Pinoccio/hardware-pinoccio/firmware/bootloader/uracoli-src-20131127/inc/const.h

/* Copyright (c) 2007 - 2013
    Marco Arena
    Axel Wachtler

   All rights reserved.

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
   THIS SOFTWARE IS PROVIDED BY THE COPYRIGHT HOLDERS AND CONTRIBUTORS "AS IS"
   AND ANY EXPRESS OR IMPLIED WARRANTIES, INCLUDING, BUT NOT LIMITED TO, THE
   IMPLIED WARRANTIES OF MERCHANTABILITY AND FITNESS FOR A PARTICULAR PURPOSE
   ARE DISCLAIMED. IN NO EVENT SHALL THE COPYRIGHT OWNER OR CONTRIBUTORS BE
   LIABLE FOR ANY DIRECT, INDIRECT, INCIDENTAL, SPECIAL, EXEMPLARY, OR
   CONSEQUENTIAL DAMAGES (INCLUDING, BUT NOT LIMITED TO, PROCUREMENT OF
   SUBSTITUTE GOODS OR SERVICES; LOSS OF USE, DATA, OR PROFITS; OR BUSINESS
   INTERRUPTION) HOWEVER CAUSED AND ON ANY THEORY OF LIABILITY, WHETHER IN
   CONTRACT, STRICT LIABILITY, OR TORT (INCLUDING NEGLIGENCE OR OTHERWISE)
   ARISING IN ANY WAY OUT OF THE USE OF THIS SOFTWARE, EVEN IF ADVISED OF THE
   POSSIBILITY OF SUCH DAMAGE. */

/* $Id$ */
/**
 * @file
 * @brief General Definitions.
 *
 */
/*====================================================================*/
#ifndef CONST_H
#define CONST_H
#include <stdint.h>
#include <stdbool.h>

/*=== board type constants ===================================================*/
/**
 * @addtogroup grpBoard
 * @{
 */

#define BOARD_NONE (0)

/* the legacy boards are sorted alphabetically */
#define BOARD_ANY2400 (1)
#define BOARD_ANY2400ST (2)
#define BOARD_ANY900 (3)
#define BOARD_ANY900ST (4)
#define BOARD_BAT (5)
#define BOARD_BITBEAN (6)
#define BOARD_CBB212 (7)
#define BOARD_CBB230 (8)
#define BOARD_CBB230B (9)
#define BOARD_CBB231 (10)
#define BOARD_CBB232 (11)
#define BOARD_CBB233 (12)
#define BOARD_DERFA1 (13)
#define BOARD_DERFTORCBRFA1 (14)
#define BOARD_DRACULA (15)
#define BOARD_IBDT212 (16)
#define BOARD_IBDT231 (17)
#define BOARD_IBDT232 (18)
#define BOARD_ICM230_11 (19)
#define BOARD_ICM230_12A (20)
#define BOARD_ICM230_12B (21)
#define BOARD_ICM230_12C (22)
#define BOARD_ICS230_11 (23)
#define BOARD_ICS230_12 (24)
#define BOARD_ICT230 (25)
#define BOARD_IM240A (26)
#define BOARD_IM240A_EVAL (27)
#define BOARD_LGEE231 (28)
#define BOARD_LGEE231_V2 (29)
#define BOARD_MIDGEE (30)
#define BOARD_MNB900 (31)
#define BOARD_MUSE231 (32)
#define BOARD_MUSEII232 (33)
#define BOARD_MUSEIIRFA (34)
#define BOARD_PINOCCIO (35)
#define BOARD_PSK212 (36)
#define BOARD_PSK230 (37)
#define BOARD_PSK230B (38)
#define BOARD_PSK231 (39)
#define BOARD_PSK232 (40)
#define BOARD_PSK233 (41)
#define BOARD_RADIOFARO (42)
#define BOARD_RADIOFARO_V1 (43)
#define BOARD_RAVRF230A (44)
#define BOARD_RAVRF230B (45)
#define BOARD_RBB128RFA1 (46)
#define BOARD_RBB212 (47)
#define BOARD_RBB230 (48)
#define BOARD_RBB230B (49)
#define BOARD_RBB231 (50)
#define BOARD_RBB232 (51)
#define BOARD_RBB233 (52)
#define BOARD_RDK212 (53)
#define BOARD_RDK230 (54)
#define BOARD_RDK230B (55)
#define BOARD_RDK231 (56)
#define BOARD_RDK232 (57)
#define BOARD_RDK233 (58)
#define BOARD_ROSE231 (59)
#define BOARD_RZUSB (60)
#define BOARD_STB128RFA1 (61)
#define BOARD_STB212 (62)
#define BOARD_STB230 (63)
#define BOARD_STB230B (64)
#define BOARD_STB231 (65)
#define BOARD_STB232 (66)
#define BOARD_STB233 (67)
#define BOARD_STKM16 (68)
#define BOARD_STKM8 (69)
#define BOARD_TINY230 (70)
#define BOARD_TINY231 (71)
#define BOARD_WDBA1281 (72)
#define BOARD_WPROG (73)
#define BOARD_XXO (74)
#define BOARD_ZGBH212 (75)
#define BOARD_ZGBH230 (76)
#define BOARD_ZGBH231 (77)
#define BOARD_ZGBL212 (78)
#define BOARD_ZGBL230 (79)
#define BOARD_ZGBL231 (80)
#define BOARD_ZGBT1281A2NOUART (81)
#define BOARD_ZGBT1281A2UART0 (82)
#define BOARD_ZGBT1281A2UART1 (83)
#define BOARD_ZIGDUINO (84)

/* beyond this point the boards are added chronologically */
#define BOARD_STB256RFR2 (85)
#define BOARD_RASPBEE (86)
#define BOARD_DERFN256U0 (87)
#define BOARD_DERFN256U0PA (88)
#define BOARD_DERFN128 (89)
#define BOARD_DERFN128U0 (90)

#define BOARD_LAST (BOARD_RASPBEE)
/** @} */

/**
 * @addtogroup grpRadio
 * @{
 */

/*=== radio constants ================================================*/
#define  RADIO_AT86RF230 (1) /**< Identifier for radio AT86RF230 */
#define  RADIO_AT86RF230A (RADIO_AT86RF230) /**< Identifier for radio AT86RF230 Rev A */
#define  RADIO_AT86RF230B (2) /**< Identifier for radio AT86RF230 Rev B */
#define  RADIO_AT86RF231 (3) /**< Identifier for radio AT86RF231 */
#define  RADIO_AT86RF212 (4) /**< Identifier for radio AT86RF212 */
#define  RADIO_ATMEGA128RFA1_A (5) /**< Identifier for radio ATmega128RFA1 Rev. A */
#define  RADIO_ATMEGA128RFA1_B (6) /**< Identifier for radio ATmega128RFA1 Rev. B */
#define  RADIO_ATMEGA128RFA1_C (7) /**< Identifier for radio ATmega128RFA1 Rev. C */
#define  RADIO_ATMEGA128RFA1_D (8) /**< Identifier for radio ATmega128RFA1 Rev. D */
#define  RADIO_AT86RF232 (9) /**< Identifier for radio AT86RF232 */
#define  RADIO_AT86RF233 (10) /**< Identifier for radio AT86RF233 */
#define  RADIO_ATMEGA256RFR2 (11) /**< Identifier for radio ATmega128RFR2 */

#define RADIO_BAND_700 (1) /**< 700MHz frequency band (china) */
#define RADIO_BAND_800 (2) /**< 868MHz frequency band (europe)*/
#define RADIO_BAND_900 (3) /**< 900MHz frequency band (north america)*/
#define RADIO_BAND_2400 (4)  /**< 2.4GHz frequency band (international)*/

/*=== modulation schemes =====================================================*/
#define MOD_BPSK_20    (0) /**< PHY modulation BPSK, 20 kbit/s */
#define MOD_BPSK_40    (1) /**< PHY modulation BPSK, 40 kbit/s */
#define MOD_OQPSK_100  (2) /**< PHY modulation O-QPSK, 100 kbit/s */
#define MOD_OQPSK_200  (3) /**< PHY modulation O-QPSK, 200 kbit/s */
#define MOD_OQPSK_250  (4) /**< PHY modulation O-QPSK, 250 kbit/s */
#define MOD_OQPSK_400  (5) /**< PHY modulation O-QPSK, 400 kbit/s */
#define MOD_OQPSK_500  (6) /**< PHY modulation O-QPSK, 500 kbit/s */
#define MOD_OQPSK_1000 (7) /**< PHY modulation O-QPSK, 1000 kbit/s */
#define MOD_OQPSK_2000 (8) /**< PHY modulation O-QPSK, 2000 kbit/s */

/* === sensor types ========================================================= */

typedef uint8_t sensor_const_t;

#define SENSOR_MCU_T (1)
#define SENSOR_MCU_VTG (2)
#define SENSOR_SHT21_RH (3)
#define SENSOR_SHT21_T (4)
#define SENSOR_ADXL345_ACC (5)
#define SENSOR_MMA7455_ACC (5)

/** @} */

/**
 * @addtogroup grpHIF
 * @{
 */

/*=== HIF type constants =====================================================*/
#define  HIF_NONE     (0)  /**< Identifier for no host interface */
#define  HIF_UART_0   (10) /**< Identifier for HIF type UART 0 */
#define  HIF_UART_1   (11) /**< Identifier for HIF type UART 1 */
#define  HIF_FT245    (20) /**< Identifier for HIF type USB/FT245*/
#define  HIF_AT90USB  (21) /**< Identifier for HIF type USB/ATmega1287 */

/*=== USB constants ==========================================================*/
/**
 * uracoli USB Vendor ID
 *
 * The pair of the uracoli vendor id, device id are obtained by
 *
 *  - http://www.voti.nl/pids/
 *  - http://www.frank-buss.de/pid.txt
 */
#define URACOLI_USB_VID (5824)
/**
 * uracoli USB Product ID
 * see also @ref USB_VID_URACOLI
 */
#define URACOLI_USB_PID (2183)

#define URACOLI_USB_BCD_RELEASE (0x100)
#define URACOLI_USB_VENDOR_NAME  L"URACOLI"
#define URACOLI_USB_PRODUCT_NAME L"RZUSBSTICK"

/** @} */

/**
 * @addtogroup grpTrx
 * @{
 */

/*=== spi constants ==========================================================*/
#define SPI_RATE_1_2      (4) /**< SPI clock running is 0.5 (1/2) of cpu clock */
#define SPI_RATE_1_4      (0) /**< SPI clock running is 0.25 (1/4) of cpu clock */
#define SPI_RATE_1_8      (5) /**< SPI clock running is 0.125 (1/8) of cpu clock */
#define SPI_RATE_1_16     (1) /**< SPI clock running is 0.0635 (1/16) of cpu clock */
#define SPI_RATE_1_32     (6) /**< SPI clock running is 0.03125 (1/32)of cpu clock */
#define SPI_RATE_1_64     (2) /**< SPI clock running is 0.015625 (1/64)of cpu clock */
#define SPI_RATE_1_128    (3) /**< SPI clock running is 0.0078125 (1/128) of cpuclock */

/** @} */


#if defined (DOXYGEN)
/** macro that forces an enumeration to use 8 bit instead of 16 bit integers. */
#define SHORTENUM
#else
#define SHORTENUM  __attribute__((packed))
#endif

/**
 * @addtogroup grpTrx
 * @{
 */
#define FCTL_DATA _BV(0)        /**< data frame fype in frame control field */
#define FCTL_ACK  _BV(5)        /**< ack request in frame control field */
#define FCTL_IPAN _BV(6)        /**< intra pan bit in frame control field */
#define FCTL_DST_SHORT 0x0800   /**< destination short address in frame control field */
#define FCTL_DST_LONG  0x0c00   /**< destination long address in frame control field */
#define FCTL_SRC_SHORT 0x8000   /**< source short address in frame control field */
#define FCTL_SRC_LONG  0xc000   /**< source long address in frame control field */

#define FCTL_SRC_MASK (FCTL_SRC_LONG)
#define FCTL_DST_MASK (FCTL_DST_LONG)
#define FCTL_IPAN_MASK (FCTL_IPAN)
/** @} */

/* === Types ================================================================ */


/**
 * @addtogroup grpTrx
 * @{
 */

/** transceiver channel type */
typedef int8_t  channel_t;

/** transceiver transmit type */
typedef int8_t  txpwr_t;

/** radio idle state, if true radio idles in state PX_ON
 *  @todo make it state_t variable, so that idle state can explicitely selected.
 */
typedef bool    rxidle_t;

/** transceiver cca mode, 1 : ED, 2: CS, 3: CS & ED */
typedef uint8_t ccamode_t;

/* ... cca_ed_tresh, clkm, pdt, ... */

/**
 * Transceiver parameter structure
 */
typedef struct
{
    /** current channel see sub register @ref SR_CHANNEL*/
    channel_t chan;
    /**  TX power index see sub register @ref SR_TX_PWR*/
    unsigned int txp   : 4;
    /**  CCA mode see sub register @ref SR_CCA_MODE */
    unsigned int cca   : 2;
    /**  ED threshold see sub register @ref SR_CCA_ED_THRES */
    unsigned int edt   : 4;

    /**  clkm control  see sub register @ref SR_CLKM_CTRL */
    unsigned int clkm  : 3;

} trx_param_t;

/** @} */
#endif  /* #ifndef CONST_H */
